Franck78/BIPOLAR-PROM-PROG/images/assembled-top.jpg

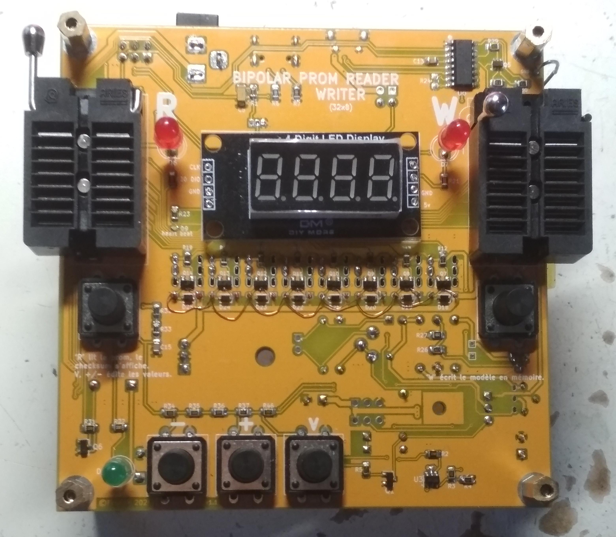
images/assembled-top.jpg
